chihyunan/arv-e_stop-pcb/ESP32_Dev_2018-4.sch

## EAGLE design ESP32_Dev_2018-4.sch (2026-02-27)

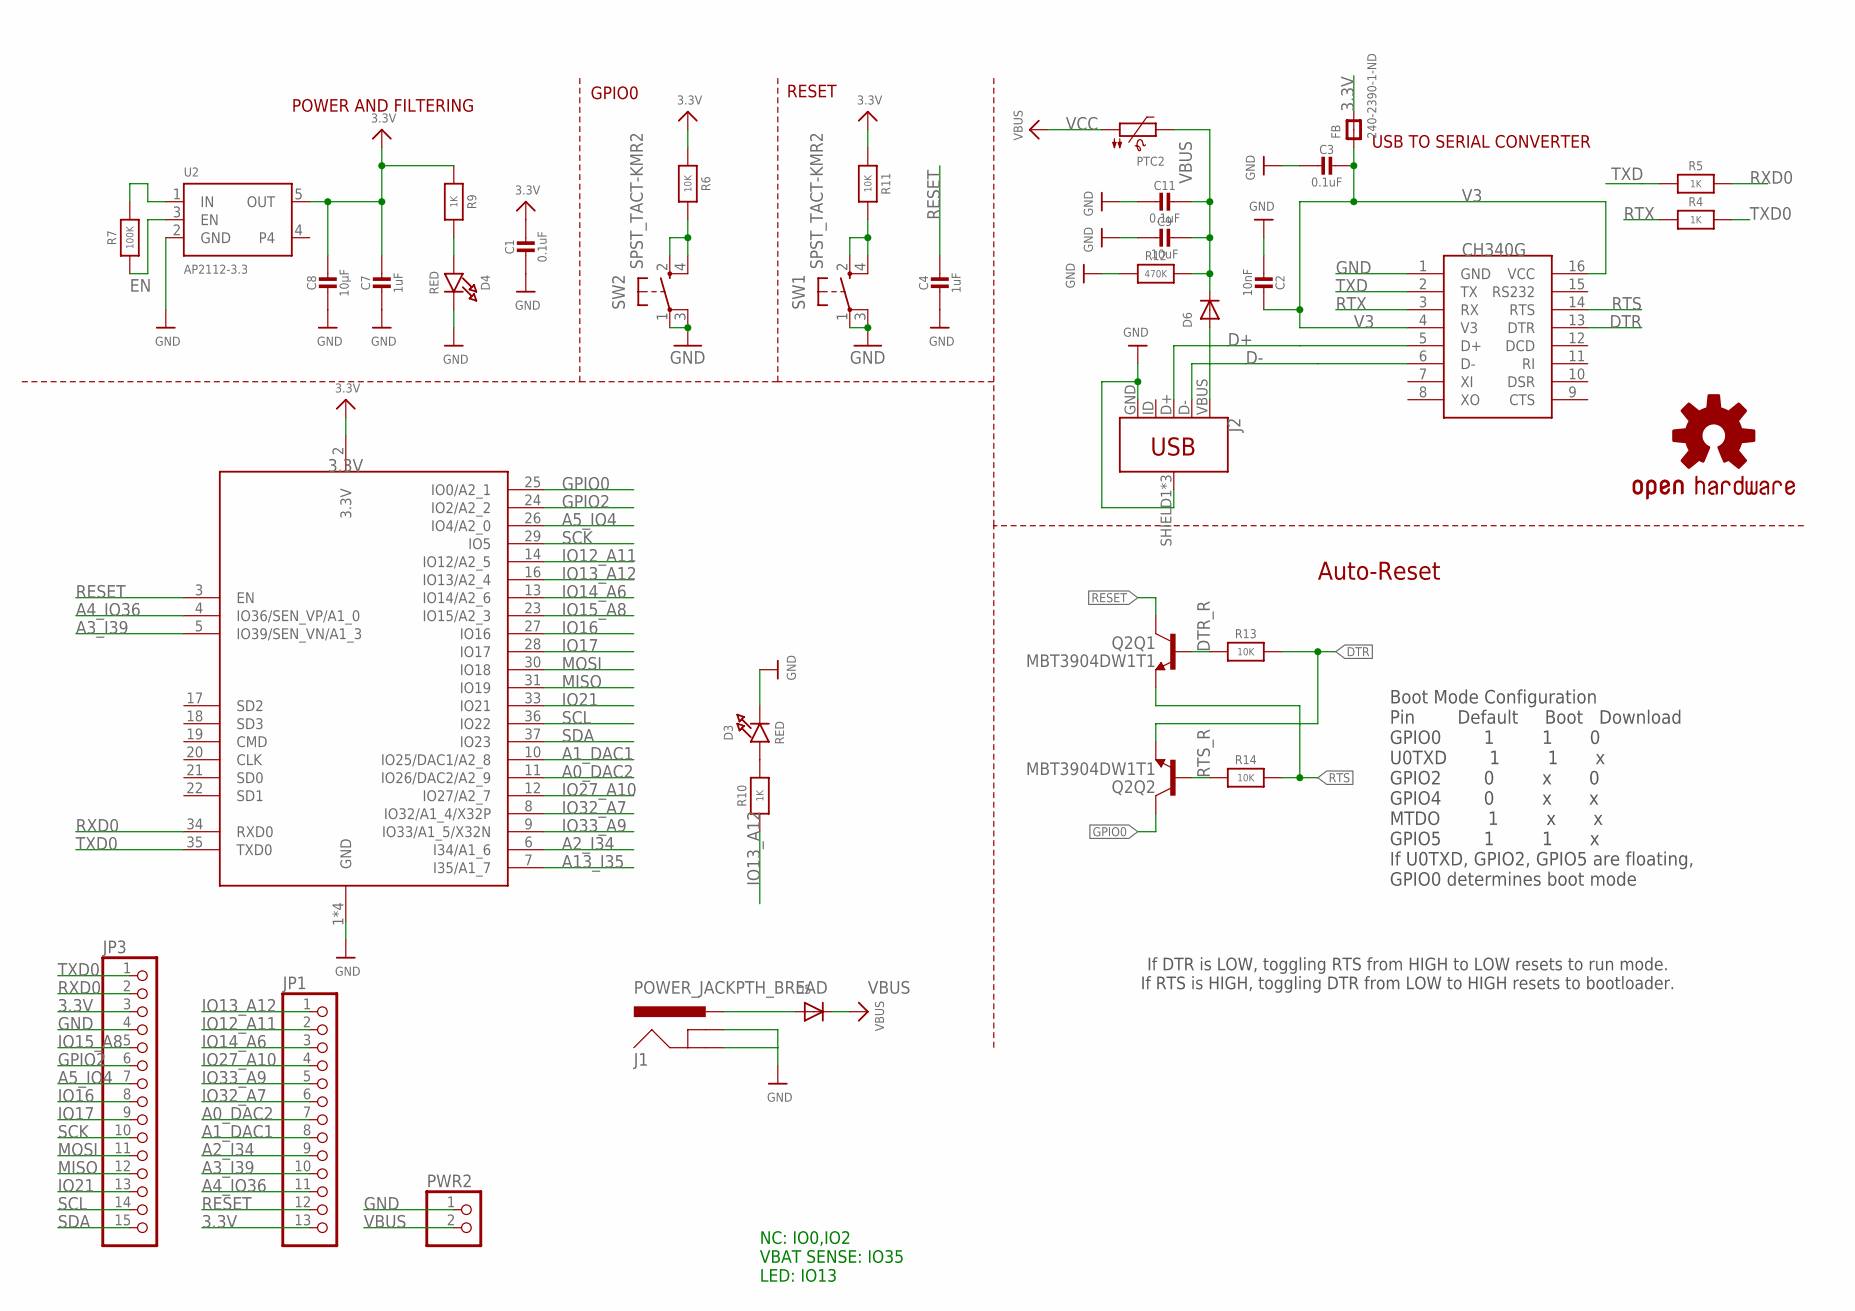
[picture p8: schematic ESP32_Dev_2018-4.sch]

Parts:
C1, C3, C11: 0.1uF; 0805-NO
C2: 10nF; 0805-NO
C4, C7: 1uF; 0805-NO
C8: 10µF; 0805-NO
C9: 10uF; 0805-NO
CH340C: CH340C; SOIC16
D3, D4: RED; CHIPLED_0805_NOOUTLINE
D5, D6: DIODESOD-123; SOD-123
FB: 240-2390-1-ND; _0805
J1: POWER_JACKPTH_BREAD; POWER_JACK_PTH_BREAD
J2: USB_MICRO-BREDUCED_PASTE; USB-B-MICRO-SMD_RED_PASTE
JP1: HEADER-1X13; 1X13_ROUND_70
JP3: HEADER-1X15; 1X15_ROUND_70
LOGO1: OSHW-LOGOM; OSHW-LOGO-M
PTC2: PTC1206; 1206
PWR2: HEADER-1X2ROUND; 1X02_ROUND
Q2: MBT3904DW1T1; SC70-6
R4, R5, R9, R10: 1K; 0805-NO
R6, R11, R13, R14: 10K; 0805-NO
R7: 100K; 0805-NO
R12: 470K; 0805-NO
SW1, SW2: SPST_TACT-KMR2; KMR2
U2: AP2112-3.3; SOT23-5
X2: ESP32_WROOM32; WROOM32

Connections:
3.3V: C1.1, C7.1, C8.1, FB.2, JP1.13, JP3.3, R6.1, R9.1, R11.1, U2.5 (OUT), X2.2 (3.3V)
A0_DAC2: JP1.7, X2.11 (IO26/DAC2/A2_9)
A1_DAC1: JP1.8, X2.10 (IO25/DAC1/A2_8)
A2_I34: JP1.9, X2.6 (I34/A1_6)
A3_I39: JP1.10, X2.5 (IO39/SEN_VN/A1_3)
A4_IO36: JP1.11, X2.4 (IO36/SEN_VP/A1_0)
A5_IO4: JP3.7, X2.26 (IO4/A2_0)
A13_I35: X2.7 (I35/A1_7)
D+: CH340C.5 (D+), J2.D+
D-: CH340C.6 (D-), J2.D-
DTR: CH340C.13 (DTR), Q2.1 (E), R13.2
DTR_R: Q2.5 (B), R13.1
EN: R7.1, U2.3 (EN)
GND: C1.2, C2.2, C3.2, C4.2, C7.2, C8.2, C9.2, C11.2, CH340C.1 (GND), D3.C, D4.C, J1.GND, J1.GNDBREAK, J2.GND, J2.SHIELD1 (SHIELD), JP3.4, PWR2.1, R12.1, SW1.1, SW1.3 (P1), SW2.1, SW2.3 (P1), U2.2 (GND), X2.1 (GND)
GPIO0: Q2.6 (C), R6.2, SW2.2 (S), SW2.4 (S1), X2.25 (IO0/A2_1)
GPIO2: JP3.6, X2.24 (IO2/A2_2)
IO12_A11: JP1.2, X2.14 (IO12/A2_5)
IO13_A12: JP1.1, R10.1, X2.16 (IO13/A2_4)
IO14_A6: JP1.3, X2.13 (IO14/A2_6)
IO15_A8: JP3.5, X2.23 (IO15/A2_3)
IO16: JP3.8, X2.27 (IO16)
IO17: JP3.9, X2.28 (IO17)
IO21: JP3.13, X2.33 (IO21)
IO27_A10: JP1.4, X2.12 (IO27/A2_7)
IO32_A7: JP1.6, X2.8 (IO32/A1_4/X32P)
IO33_A9: JP1.5, X2.9 (IO33/A1_5/X32N)
MISO: JP3.12, X2.31 (IO19)
MOSI: JP3.11, X2.30 (IO18)
unnamed: D6.A, J2.VBUS
unnamed: D3.A, R10.2
unnamed: D4.A, R9.2
RESET: C4.1, JP1.12, Q2.3 (C), R11.2, SW1.2 (S), SW1.4 (S1), X2.3 (EN)
RTS: CH340C.14 (RTS), Q2.4 (E), R14.2
RTS_R: Q2.2 (B), R14.1
RTX: CH340C.3 (RX), R4.1
RXD0: JP3.2, R5.2, X2.34 (RXD0)
SCK: JP3.10, X2.29 (IO5)
SCL: JP3.14, X2.36 (IO22)
SDA: JP3.15, X2.37 (IO23)
TXD: CH340C.2 (TX), R5.1
TXD0: JP3.1, R4.2, X2.35 (TXD0)
V3: C2.1, C3.1, CH340C.4 (V3), CH340C.16 (VCC), FB.1
VBUS: C9.1, C11.1, D5.C, D6.C, PTC2.2, PWR2.2, R12.2
VBUS1: D5.A, J1.PWR
VCC: PTC2.1, R7.2, U2.1 (IN)

Notes on the sheet:
POWER AND FILTERING
RESET
USB TO SERIAL CONVERTER
NC: IO0,IO2 VBAT SENSE: IO35 LED: IO13
Boot Mode Configuration Pin Default Boot Download GPIO0 1 1 0 U0TXD 1 1 x GPIO2 0 x 0 GPIO4 0 x x MTDO 1 x x GPIO5 1 1 x If U0TXD, GPIO2, GPIO5 are floating, GPIO0 determines boot mode
Auto-Reset
If DTR is LOW, toggling RTS from HIGH to LOW resets to run mode. If RTS is HIGH, toggling DTR from LOW to HIGH resets to bootloader.
GPIO0
